luisllamasbinaburo/OpenRobot/OpenRobot/Images/OpenRobot-pcb.jpg

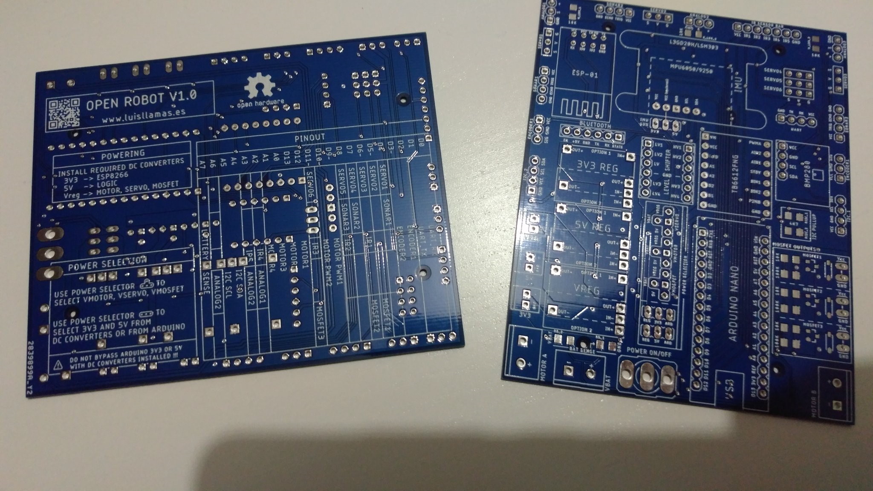
OpenRobot/Images/OpenRobot-pcb.jpg
